EbrithilNogare/AirAnalyzer/graphics/cloud.png

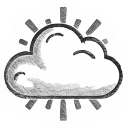
graphics/cloud.png
