EbrithilNogare/AirAnalyzer/graphics/moon/1.png

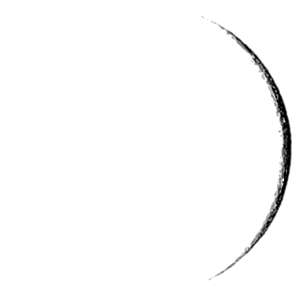
graphics/moon/1.png
