EbrithilNogare/AirAnalyzer/graphics/moon/6.png

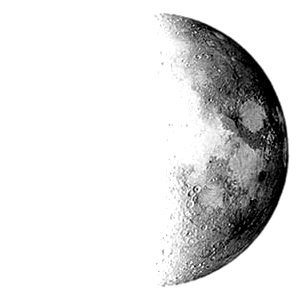
graphics/moon/6.png
