EbrithilNogare/AirAnalyzer/graphics/moon/9.png

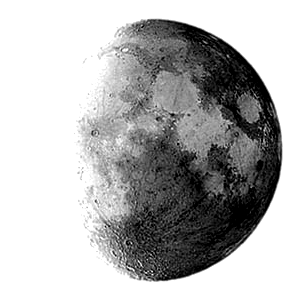
graphics/moon/9.png
