EbrithilNogare/AirAnalyzer/graphics/moon/10.png

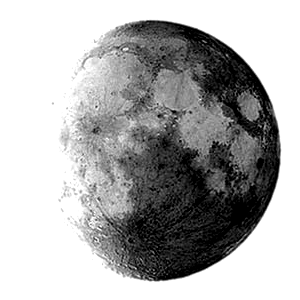
graphics/moon/10.png
