EbrithilNogare/AirAnalyzer/graphics/moon/12.png

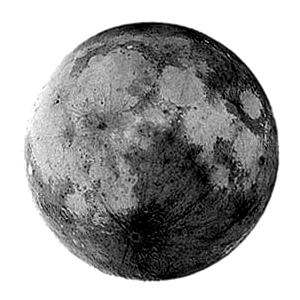
graphics/moon/12.png
