EbrithilNogare/AirAnalyzer/graphics/moon/14.png

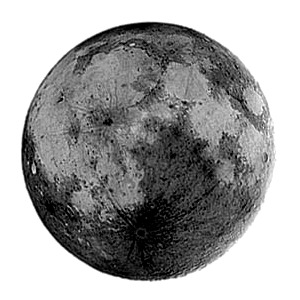
graphics/moon/14.png
