EbrithilNogare/AirAnalyzer/graphics/moon/16.png

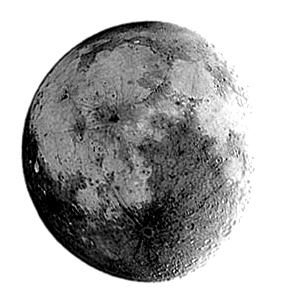
graphics/moon/16.png
