EbrithilNogare/AirAnalyzer/graphics/moon/17.png

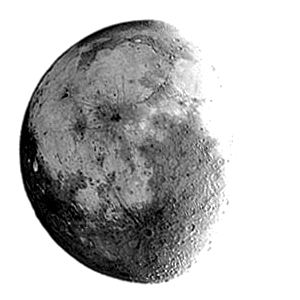
graphics/moon/17.png
