EbrithilNogare/AirAnalyzer/graphics/moon/18.png

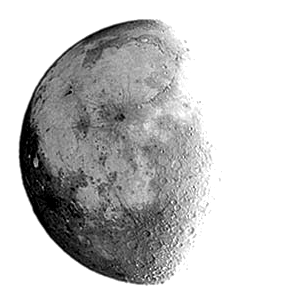
graphics/moon/18.png
