EbrithilNogare/AirAnalyzer/graphics/moon/19.png

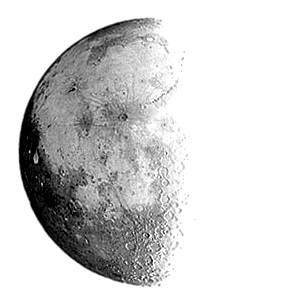
graphics/moon/19.png
