EbrithilNogare/AirAnalyzer/graphics/moon/20.png

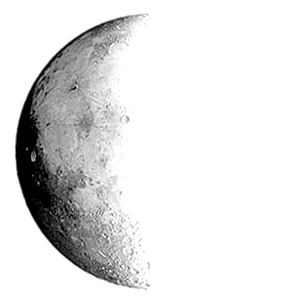
graphics/moon/20.png
