EbrithilNogare/AirAnalyzer/graphics/moon/21.png

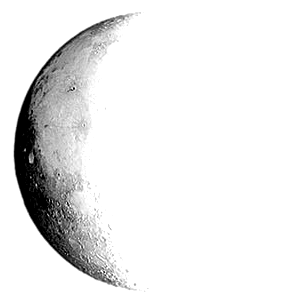
graphics/moon/21.png
