EbrithilNogare/AirAnalyzer/graphics/moon/22.png

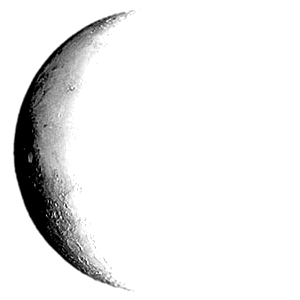
graphics/moon/22.png
