EbrithilNogare/AirAnalyzer/graphics/moon/23.png

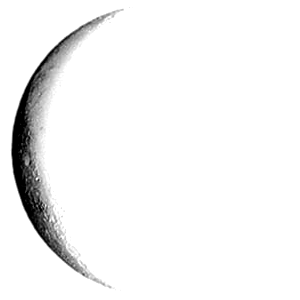
graphics/moon/23.png
