EbrithilNogare/AirAnalyzer/graphics/storm.png

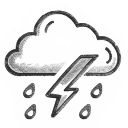
graphics/storm.png
