EbrithilNogare/AirAnalyzer/graphics/sun.png

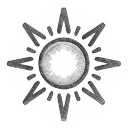
graphics/sun.png
