EbrithilNogare/AirAnalyzer/src/rendering.cpp

#include "rendering.h"
#include "icons/temp.icon.h"
#include "icons/humidity.icon.h"
#include "icons/pressure.icon.h"
#include "icons/sunrise.icon.h"
#include "icons/sunset.icon.h"
#include "icons/co2.icon.h"
#include "icons/moon.icon.h"

inline void drawDashedHLine(DisplayType& display, int x1, int x2, int y, int onLen = 3, int offLen = 3) {
	for (int xx = x1; xx <= x2; xx += onLen + offLen) {
		int segW = std::min(onLen, x2 - xx + 1);
		if (segW > 0)
			display.drawLine(xx, y, xx + segW - 1, y, GxEPD_BLACK);
	}
}

inline void drawDashedVLine(DisplayType& display, int y1, int y2, int x, int onLen = 3, int offLen = 3) {
	for (int yy = y1; yy <= y2; yy += onLen + offLen) {
		int segH = std::min(onLen, y2 - yy + 1);
		if (segH > 0)
			display.drawLine(x, yy, x, yy + segH - 1, GxEPD_BLACK);
	}
}

const uint8_t ditherPatterns[8][4] = {
	{0b1111, 0b1111, 0b1111, 0b1111},
	{0b1111, 0b0111, 0b1111, 0b1101},
	{0b1010, 0b1111, 0b1010, 0b1111},
	{0b1010, 0b0101, 0b1010, 0b0101},
	{0b1010, 0b0000, 0b0101, 0b0000},
	{0b1000, 0b0000, 0b0010, 0b0000},
	{0b0000, 0b0100, 0b0000, 0b0000},
	{0b0000, 0b0000, 0b0000, 0b0000},
};

inline bool shouldDrawPixel(int x, int y, int ditherLevel) {
	if (ditherLevel >= 8) return false;
	if (ditherLevel < 0) ditherLevel = 0;
	int px = x % 4;
	int py = y % 4;
	return (ditherPatterns[ditherLevel][py] >> (3 - px)) & 1;
}

// Catmull-Rom spline: smooth curve that passes exactly through every data point.
// fi is a fractional index into data[0..n-1]; at whole indices it returns data[i] exactly.
inline float catmullRom(const float* d, int n, float fi) {
	if (n <= 1) return d[0];
	if (fi <= 0.0f) return d[0];
	if (fi >= n - 1) return d[n - 1];
	int i1 = static_cast<int>(fi);
	float t = fi - i1;
	int i0 = std::max(0, i1 - 1);
	int i2 = std::min(n - 1, i1 + 1);
	int i3 = std::min(n - 1, i1 + 2);
	float p0 = d[i0], p1 = d[i1], p2 = d[i2], p3 = d[i3];
	float t2 = t * t, t3 = t2 * t;
	return 0.5f * ((2.0f * p1) + (-p0 + p2) * t + (2.0f * p0 - 5.0f * p1 + 4.0f * p2 - p3) * t2 + (-p0 + 3.0f * p1 - 3.0f * p2 + p3) * t3);
}

// A rain data point is "active" (drawn) if it or an immediate neighbour has rain,
// so a run of rain is bounded by exactly one zero point on each side.
inline bool rainActiveIdx(const float* d, int n, int i) {
	if (i < 0 || i >= n) return false;
	if (d[i] > 0.0f) return true;
	if (i > 0 && d[i - 1] > 0.0f) return true;
	if (i < n - 1 && d[i + 1] > 0.0f) return true;
	return false;
}

// Bottom padding of the temperature plot: keeps the lowest point high enough that the shadow fade (3 px gap + fadeDepth) below it isn't clipped at the graph edge.
const int tempGraphBottomPad = 27;

void drawForecastGraph(DisplayType& display, int x, int y, int w, int h, const float* data, int dataSize, float minVal, float maxVal) {
	float range = maxVal - minVal;
	if (range <= 0.001f) range = 1.0f;
	int n = dataSize;
	int xEnd = x + (n - 1) * w / n; // pixel x of the last data point
	int plotH = h - tempGraphBottomPad;

	auto valToY = [&](float v) {
		return y + plotH - static_cast<int>(((v - minVal) / range) * plotH);
	};
	auto splineYclamped = [&](int px) {
		float fi = static_cast<float>(px - x) * n / w;
		return std::max(y, std::min(y + h - 1, valToY(catmullRom(data, n, fi))));
	};

	int zeroY = valToY(0.0f);
	bool zeroInRange = (zeroY >= y && zeroY <= y + h);

	const int fadeDepth = 24;
	const int fadeSteps = 8;

	// Shadow fade beneath the smooth spline
	for (int px = x; px <= xEnd; px++) {
		float fi = static_cast<float>(px - x) * n / w;
		float val = catmullRom(data, n, fi);
		int currentY = std::max(y, std::min(y + h - 1, valToY(val)));
		bool aboveZero = val >= 0;

		if (aboveZero) {
			int trailEnd = zeroInRange ? std::min(zeroY, y + h - 1) : y + h - 1;
			trailEnd = std::min(trailEnd, currentY + fadeDepth);
			for (int py = currentY + 3; py <= trailEnd; py++) {
				int dist = py - currentY;
				int ditherLevel = (dist * fadeSteps) / fadeDepth;
				if (shouldDrawPixel(px, py, ditherLevel)) display.drawPixel(px, py, GxEPD_BLACK);
			}
		} else {
			int trailEnd = zeroInRange ? std::max(zeroY, y) : y;
			trailEnd = std::max(trailEnd, currentY - fadeDepth);
			for (int py = currentY - 3; py >= trailEnd; py--) {
				int dist = currentY - py;
				int ditherLevel = (dist * fadeSteps) / fadeDepth;
				if (shouldDrawPixel(px, py, ditherLevel)) display.drawPixel(px, py, GxEPD_BLACK);
			}
		}
	}

	int firstLine = static_cast<int>(floor(minVal / 10.0f)) * 10;
	for (int t = firstLine; t <= static_cast<int>(ceil(maxVal)); t += 10) {
		int yy = valToY(static_cast<float>(t));
		if (yy < y || yy > y + h) continue;
		if (t == 0) {
			display.drawLine(x + 1, yy - 1, x + w - 2, yy - 1, GxEPD_BLACK);
			display.drawLine(x + 1, yy, x + w - 2, yy, GxEPD_BLACK);
			display.drawLine(x + 1, yy + 1, x + w - 2, yy + 1, GxEPD_BLACK);
		} else {
			display.drawLine(x + 1, yy, x + w - 2, yy, GxEPD_BLACK);
		}
	}

	// Thick smooth spline line (fill between adjacent columns so steep slopes stay solid)
	for (int px = x; px < xEnd; px++) {
		int y0 = splineYclamped(px);
		int y1 = splineYclamped(px + 1);
		int lo = std::min(y0, y1);
		int hi = std::max(y0, y1);
		for (int py = lo - 2; py <= hi + 2; py++) {
			if (py >= y && py <= y + h - 1) display.drawPixel(px, py, GxEPD_BLACK);
		}
	}
}

void drawApparentTempLine(DisplayType& display, int x, int y, int w, int h, const float* data, int dataSize, float minVal, float maxVal) {
	float range = maxVal - minVal;
	if (range <= 0.001f) range = 1.0f;
	int n = dataSize;
	int xEnd = x + (n - 1) * w / n;
	int plotH = h - tempGraphBottomPad; // same mapping as drawForecastGraph so both lines stay aligned

	auto splineYclamped = [&](int px) {
		float fi = static_cast<float>(px - x) * n / w;
		int yy = y + plotH - static_cast<int>(((catmullRom(data, n, fi) - minVal) / range) * plotH);
		return std::max(y, std::min(y + h - 1, yy));
	};

	for (int px = x; px < xEnd; px++) {
		int y0 = splineYclamped(px);
		int y1 = splineYclamped(px + 1);
		int lo = std::min(y0, y1);
		int hi = std::max(y0, y1);

		// 2px dash, 2px gap pattern; draw white for gap to erase what is underneath
		bool isDash = ((px - x) % 4) < 2;
		uint16_t color = isDash ? GxEPD_BLACK : GxEPD_WHITE;

		// 2 pixels thick, filling between adjacent columns so the dots stay connected on slopes
		for (int py = lo; py <= hi + 1; py++) {
			if (py >= y && py <= y + h - 1) display.drawPixel(px, py, color);
		}
	}
}

void drawRainLine(DisplayType& display, int x, int y, int w, int h, const float* data, int dataSize, float maxVal) {
	if (maxVal <= 0.001f) maxVal = 1.0f;
	int n = dataSize;
	int xEnd = x + (n - 1) * w / n;

	for (int px = x; px < xEnd; px++) {
		float fi = static_cast<float>(px - x) * n / w;
		int i = static_cast<int>(fi);
		if (i < 0 || i >= n - 1) continue;
		// Draw only within an active rain region (a run of rain plus one bounding zero each side).
		if (!(rainActiveIdx(data, n, i) && rainActiveIdx(data, n, i + 1))) continue;

		float val = catmullRom(data, n, fi);
		if (val < 0.0f) val = 0.0f;
		int lineY = y + h - static_cast<int>((val / maxVal) * h);
		lineY = std::max(y, std::min(y + h, lineY));

		// Grey pattern fill from below the line down to the bottom of the band
		for (int py = lineY + 3; py <= y + h; py++) {
			if (shouldDrawPixel(px, py, 3)) display.drawPixel(px, py, GxEPD_BLACK);
		}
		// 3px thick smooth line
		for (int t = 0; t < 3; t++) {
			int py = lineY + t;
			if (py >= y && py <= y + h) display.drawPixel(px, py, GxEPD_BLACK);
		}
	}
}

void drawWeatherForecast(DisplayType& display, const float* forecastTemp, const float* forecastApparentTemp, const float* forecastRain, int forecastHours, int forecastStartHour, const String& sunriseTime, const String& sunsetTime, bool weatherDataValid) {
	if (!weatherDataValid) return;
	int screenW = display.width();
	int screenH = display.height();

	int weatherY = 8;
	int graphX = 4;
	int graphWidth = screenW - 8;
	int graphHeight = (screenH * 50) / 100;

	float minTemp = forecastTemp[0], maxTemp = forecastTemp[0];
	float maxRain = 0;
	for (int i = 0; i < forecastHours; i++) {
		if (forecastTemp[i] < minTemp) minTemp = forecastTemp[i];
		if (forecastTemp[i] > maxTemp) maxTemp = forecastTemp[i];
		if (forecastApparentTemp[i] < minTemp) minTemp = forecastApparentTemp[i];
		if (forecastApparentTemp[i] > maxTemp) maxTemp = forecastApparentTemp[i];
		if (forecastRain[i] > maxRain) maxRain = forecastRain[i];
	}
	minTemp = floor(minTemp);
	maxTemp = ceil(maxTemp);
	if (minTemp == maxTemp) { minTemp -= 1; maxTemp += 1; }

	int tempGraphY = weatherY + 28;
	int rainHeight = std::max(12, graphHeight / 3);
	int rainY = tempGraphY + graphHeight;

	drawForecastGraph(display, graphX, tempGraphY, graphWidth, graphHeight, forecastTemp, forecastHours, minTemp, maxTemp);
	drawApparentTempLine(display, graphX, tempGraphY, graphWidth, graphHeight, forecastApparentTemp, forecastHours, minTemp, maxTemp);

	display.setFont(&FreeSans12pt7b);
	int hourY = weatherY + 18;
	int lineEndY = rainY + rainHeight;
	
	for (int i = 0; i < forecastHours; i++) {
		int hour = (forecastStartHour + i) % 24;
		if (hour % 2 != 0) continue;
		int xx = graphX + i * graphWidth / forecastHours;
		
		String hlabel = String(hour);
		int16_t tbx, tby; uint16_t tbw, tbh;
		display.getTextBounds(hlabel, xx, hourY, &tbx, &tby, &tbw, &tbh);
		display.setCursor(xx - tbw / 2, hourY);
		display.print(hlabel);
		
		if (hour == 0 || hour == 12) {
			display.drawLine(xx - 1, tempGraphY + 1, xx - 1, lineEndY - 1, GxEPD_BLACK);
			display.drawLine(xx, tempGraphY + 1, xx, lineEndY - 1, GxEPD_BLACK);
			display.drawLine(xx + 1, tempGraphY + 1, xx + 1, lineEndY - 1, GxEPD_BLACK);
		} else {
			display.drawLine(xx, tempGraphY + 1, xx, lineEndY - 1, GxEPD_BLACK);
		}
	}

	display.setFont(&FreeSansBold18pt7b);
	int charWidth = 19;
	
	String maxTempStr = String(static_cast<int>(maxTemp));
	int maxLabelX = graphX + graphWidth - (maxTempStr.length() * charWidth);
	display.setCursor(maxLabelX, tempGraphY + 32);
	display.print(maxTempStr);
	
	String minTempStr = String(static_cast<int>(minTemp));
	int minLabelX = graphX + graphWidth - (minTempStr.length() * charWidth);
	display.setCursor(minLabelX, tempGraphY + graphHeight - 14);
	display.print(minTempStr);

	drawRainLine(display, graphX, rainY, graphWidth, rainHeight, forecastRain, forecastHours, max(maxRain, 1.0f));

	display.setFont(&FreeSans18pt7b);
	String rainStr = String(static_cast<int>(ceil(maxRain)));
	int rainLabelX = graphX + graphWidth - (rainStr.length() * charWidth);
	display.setCursor(rainLabelX, rainY + 40);
	display.print(rainStr);
}

void updateDisplay(
		DisplayType& display,
		float tempAir,
		float humidity,
		float co2,
		float pressure,
		const String& sunriseTime,
		const String& sunsetTime,
		const float* forecastTemp,
		const float* forecastApparentTemp,
		const float* forecastRain,
		int forecastHours,
		int forecastStartHour,
		bool weatherDataValid,
		float moonPhase,
		int batteryPercent,
		bool fullRefresh
	) {
	// A partial refresh only nudges the pixels that changed and leaves a faint copy of what it replaced,
	// so redrawing a moved graph over an old one shadows the previous curves. A full refresh drives every
	// pixel through the complete waveform and clears them, at the cost of a visible flash and ~1.9 s
	// instead of ~0.4 s. The caller spends that only when the drawing actually changes shape.
	if (fullRefresh) display.setFullWindow();
	else display.setPartialWindow(0, 0, display.width(), display.height());
	display.firstPage();
	do {
		display.fillScreen(GxEPD_WHITE);
		drawWeatherForecast(display, forecastTemp, forecastApparentTemp, forecastRain, forecastHours, forecastStartHour, sunriseTime, sunsetTime, weatherDataValid);

		int screenW = display.width();
		int screenH = display.height();
		int bottomH = std::max(64, screenH / 5);
		int bottomY = screenH - bottomH - 16;

		int icons = 7;
		int iconSize = 56;
		int gap = (screenW - icons * iconSize) / (icons + 1);
		int iconY = bottomY + 2;
		display.setFont(&FreeSans18pt7b);
		
		for (int i = 0; i < icons; i++) {
			int ix = gap + i * (iconSize + gap);
			int valY = iconY + iconSize + 18;
			String v;
			switch (i) {
				case 0: v = isnan(tempAir) ? "--" : String(tempAir, 1) + "C"; break;
				case 1: v = isnan(humidity) ? "--" : String(humidity, 0) + "%"; break;
				case 2: v = sunriseTime; break;
				case 3: v = " "; break;
				case 4: v = sunsetTime; break;
				case 5: v = isnan(co2) ? "--" : String(co2,0); break;
				case 6: v = isnan(pressure) ? "--" : String(pressure,0); break;
			}
			display.setFont(&FreeSansBold18pt7b);
			int16_t tbx, tby; uint16_t tbw, tbh;
			display.getTextBounds(v, ix + iconSize / 2, valY, &tbx, &tby, &tbw, &tbh);
			display.setCursor(ix + iconSize / 2 - tbw / 2, valY + tbh / 2);
			display.print(v);
			display.setFont(&FreeSans18pt7b);

			const int iconW = 64;
			const int iconH = 64;
			int iconDrawX = ix + (iconSize - iconW) / 2;
			int iconDrawY = iconY + (iconSize - iconH) / 2;
			switch (i) {
				case 0: display.drawBitmap(iconDrawX, iconDrawY, temp_icon_bits, iconW, iconH, GxEPD_BLACK); break;
				case 1: display.drawBitmap(iconDrawX, iconDrawY, epd_bitmap_humidity, iconW, iconH, GxEPD_BLACK); break;
				case 2: display.drawBitmap(iconDrawX, iconDrawY, epd_bitmap_sunrise, iconW, iconH, GxEPD_BLACK); break;
				case 3: {
					int moonIconIndex = static_cast<int>(moonPhase * 24.0f) % 24;
					display.drawBitmap(iconDrawX, iconDrawY+25, epd_bitmap_allArray[moonIconIndex], iconW, iconH, GxEPD_BLACK);
					break;
				}
				case 4: display.drawBitmap(iconDrawX, iconDrawY, epd_bitmap_sunset, iconW, iconH, GxEPD_BLACK); break;
				case 5: display.drawBitmap(iconDrawX, iconDrawY, epd_bitmap_co2, iconW, iconH, GxEPD_BLACK); break;
				case 6: display.drawBitmap(iconDrawX, iconDrawY, epd_bitmap_pressure, iconW, iconH, GxEPD_BLACK); break;
			}
		}

		display.setFont(&FreeSans12pt7b);
		int moonCenterX = gap + 3 * (iconSize + gap) + iconSize / 2;
		char batStr[5];
		snprintf(batStr, sizeof(batStr), "%d%%", batteryPercent);
		int16_t tbx2, tby2; uint16_t tbw2, tbh2;
		display.getTextBounds(batStr, 0, 0, &tbx2, &tby2, &tbw2, &tbh2);
		display.setCursor(moonCenterX - tbw2 / 2, screenH - 3);
		display.print(batStr);
	} while (display.nextPage());
}
